Bluescreen2001/ZX-Spectrum/SpectrumPlusKeyboard/pictures/Gehäuse_mit_Nuvo.jpg

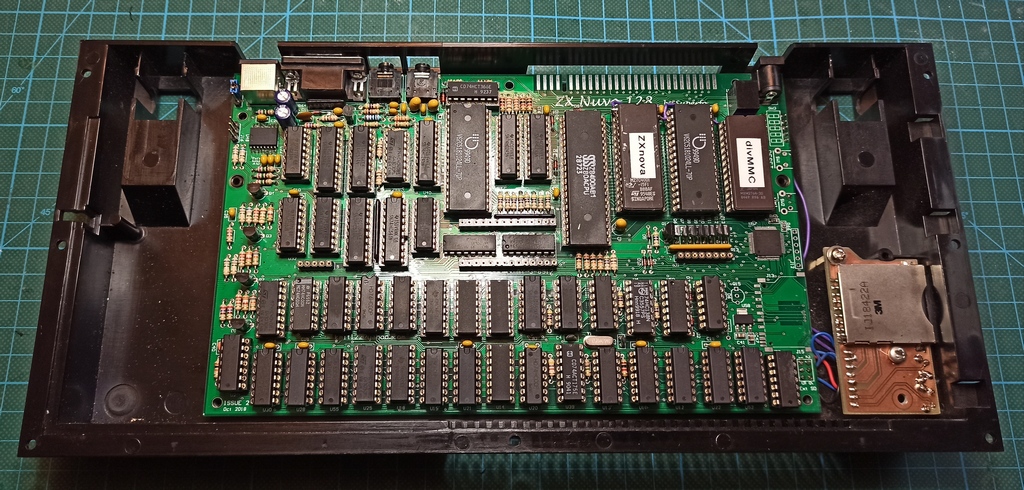
SpectrumPlusKeyboard/pictures/Gehäuse_mit_Nuvo.jpg
