Bluescreen2001/ZX-Spectrum/SpectrumPlusKeyboard/pictures/PCB-back.JPG

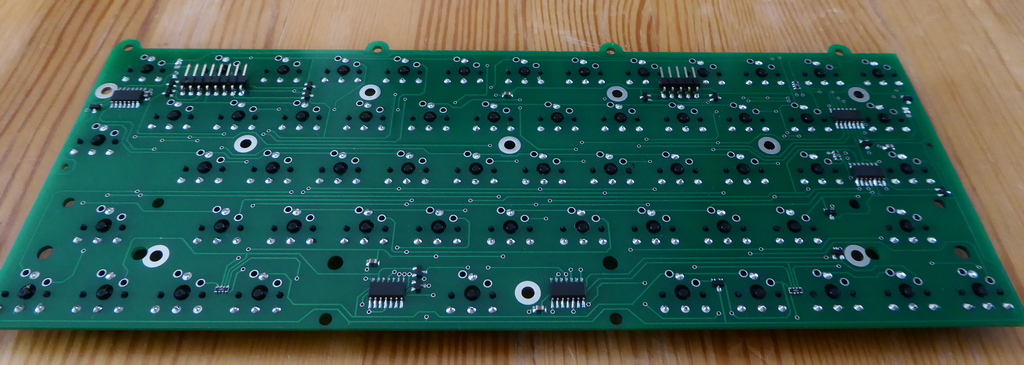
SpectrumPlusKeyboard/pictures/PCB-back.JPG
