Bluescreen2001/ZX-Spectrum/SpectrumPlusKeyboard/pictures/Platinen.jpg

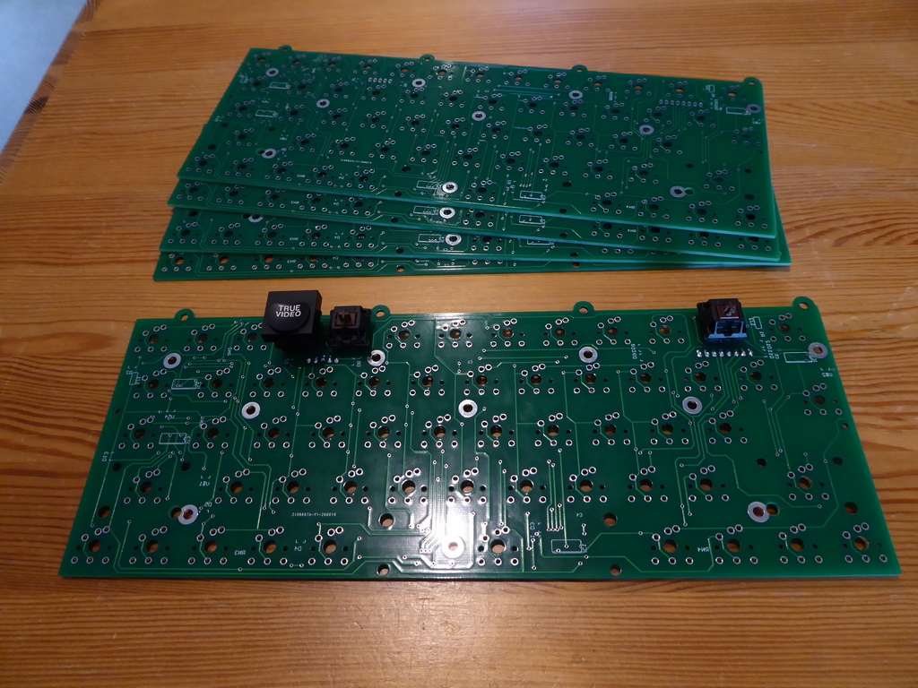
SpectrumPlusKeyboard/pictures/Platinen.jpg
