Bluescreen2001/ZX-Spectrum/SpectrumPlusKeyboard/pictures/Platinenlayout.jpg

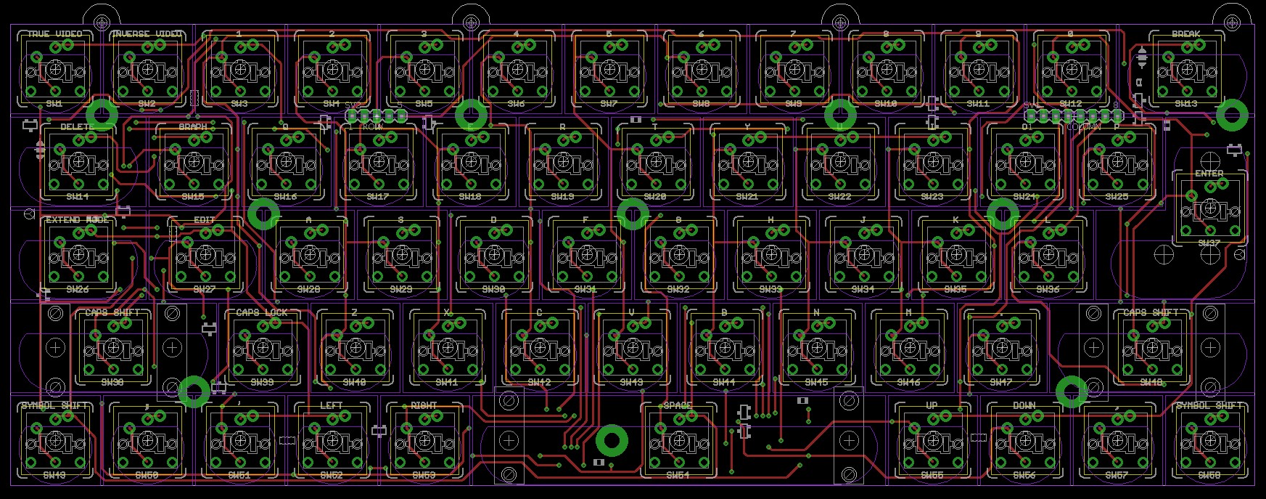
SpectrumPlusKeyboard/pictures/Platinenlayout.jpg
